ArgonPrototypes/enix-clock/CASE/Top Case - CNC Milled/Rendered Back Photo.png

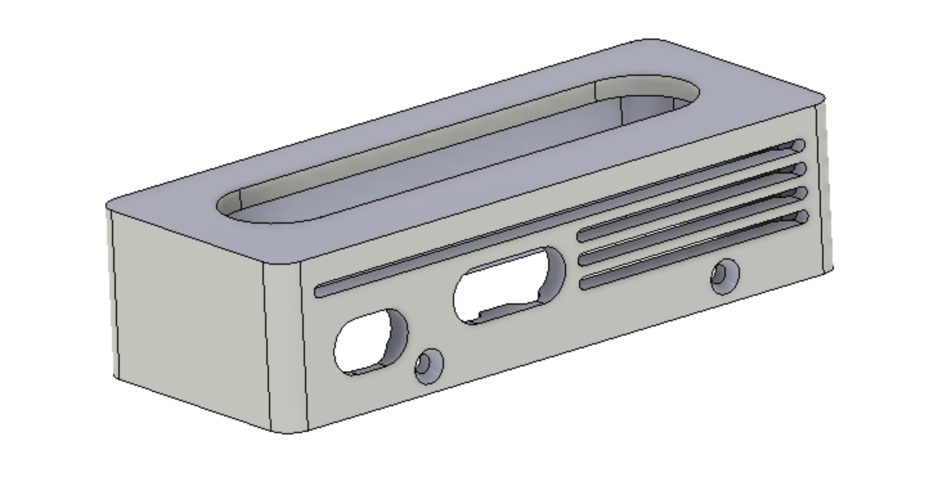
CASE/Top Case - CNC Milled/Rendered Back Photo.png
