ArgonPrototypes/enix-clock/CASE/Top Case - CNC Milled/Rendered Front Photo.png

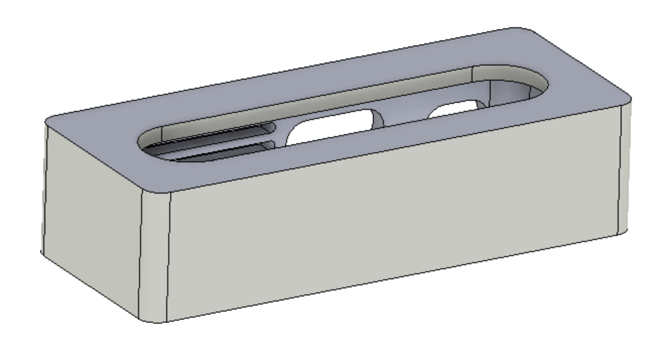
CASE/Top Case - CNC Milled/Rendered Front Photo.png
