ArgonPrototypes/enix-clock/JIGS AND ACCESSORIES/Pin Header Caps/Rendered Photo 1x8 Pin Header Cap.png

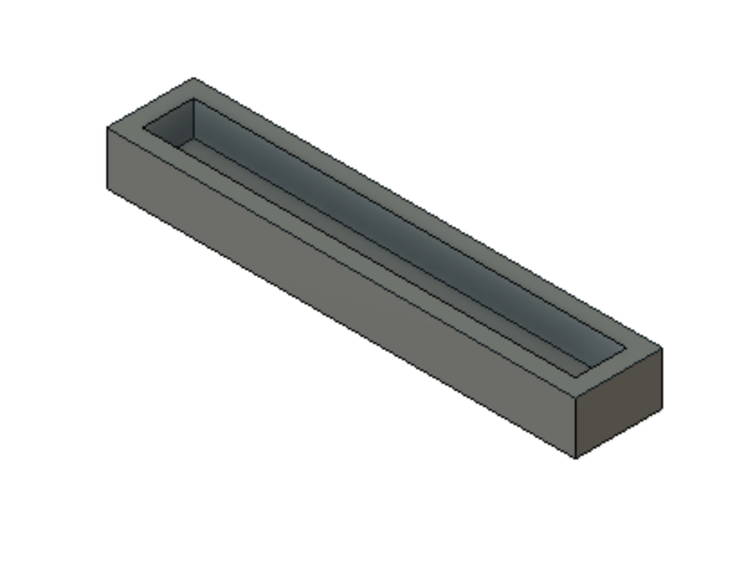
JIGS AND ACCESSORIES/Pin Header Caps/Rendered Photo 1x8 Pin Header Cap.png
