ArgonPrototypes/enix-clock/JIGS AND ACCESSORIES/Pin Header Caps/Rendered Photo 2x6 Pin Header Cap.png

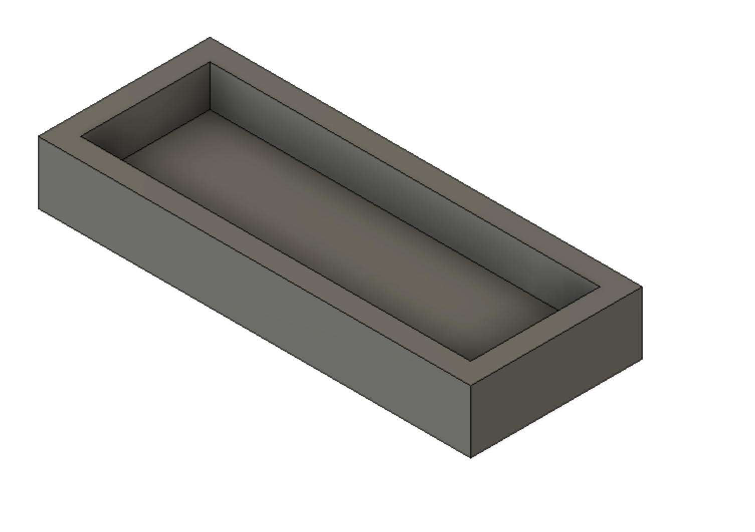
JIGS AND ACCESSORIES/Pin Header Caps/Rendered Photo 2x6 Pin Header Cap.png
