ArgonPrototypes/enix-clock/JIGS AND ACCESSORIES/Programming Jig/Jig with PCB.jpeg

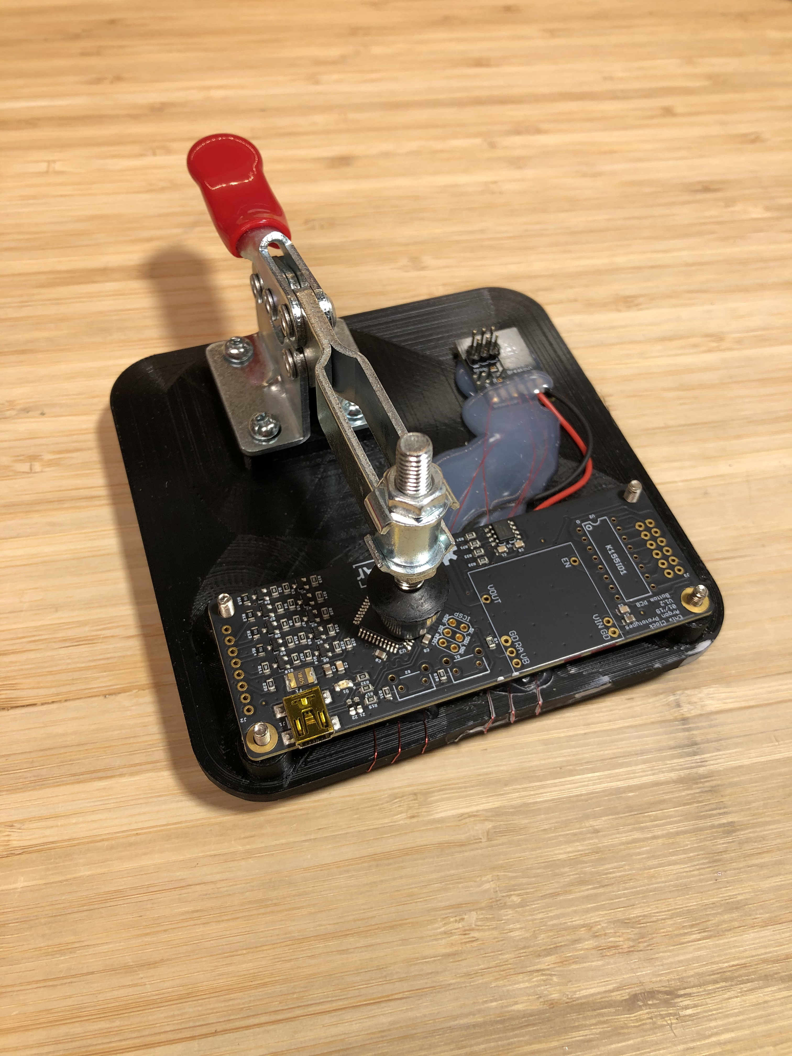
JIGS AND ACCESSORIES/Programming Jig/Jig with PCB.jpeg
