ArgonPrototypes/enix-clock/JIGS AND ACCESSORIES/Programming Jig/Rendered Photo Programming Jig.png

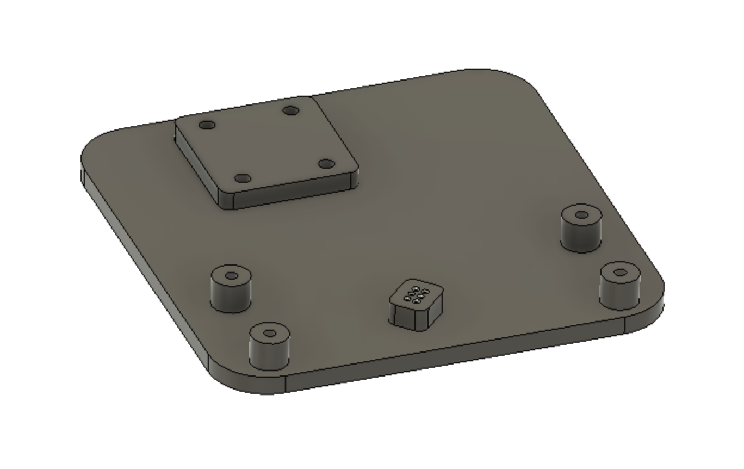
JIGS AND ACCESSORIES/Programming Jig/Rendered Photo Programming Jig.png
