ArgonPrototypes/enix-clock/PACKAGING/Bottom Foam/Rendered Photo Packaging USB Cable Side.png

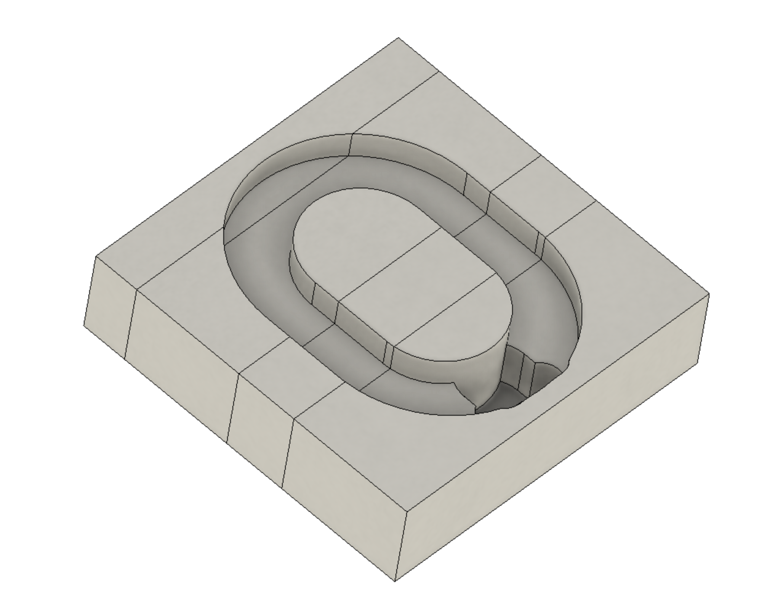
PACKAGING/Bottom Foam/Rendered Photo Packaging USB Cable Side.png
