ArgonPrototypes/enix-clock/CASE/Bottom Plate - 3D printed/Rendered Photo.png

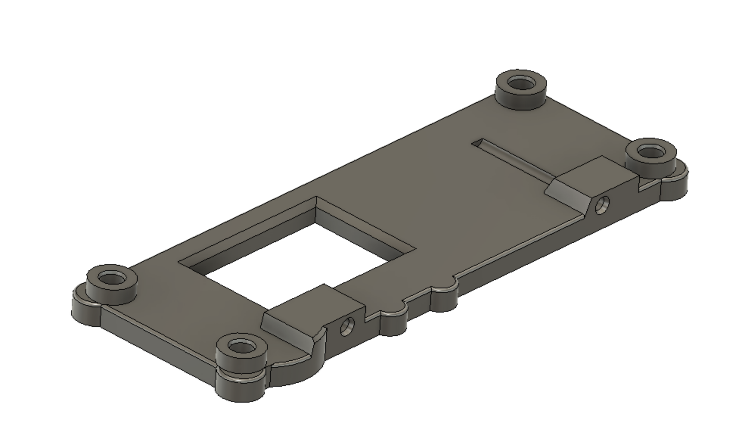
CASE/Bottom Plate - 3D printed/Rendered Photo.png
