ArgonPrototypes/enix-clock/JIGS AND ACCESSORIES/Programming Jig/Jig Open.jpeg

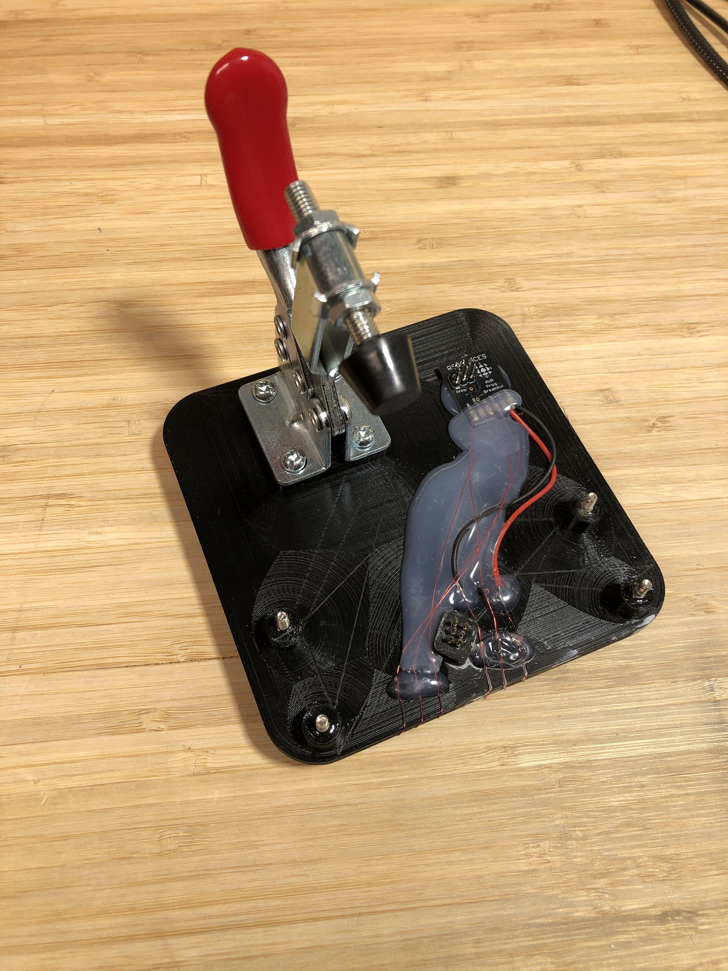
JIGS AND ACCESSORIES/Programming Jig/Jig Open.jpeg
